Antonio-Ciociola/esper/firmware/esper/main/src/utils/utils.h

#include "core/lv_obj.h"

#ifdef __cplusplus
extern "C"
{
#endif

    void style_hover(lv_obj_t *obj);
    void flex_newline(lv_obj_t *obj);
    void exit_edit_cb(lv_event_t *e);

#ifdef __cplusplus
}
#endif
